destroyer796/VoyagerSplit/Pics/3dBack12-3.png

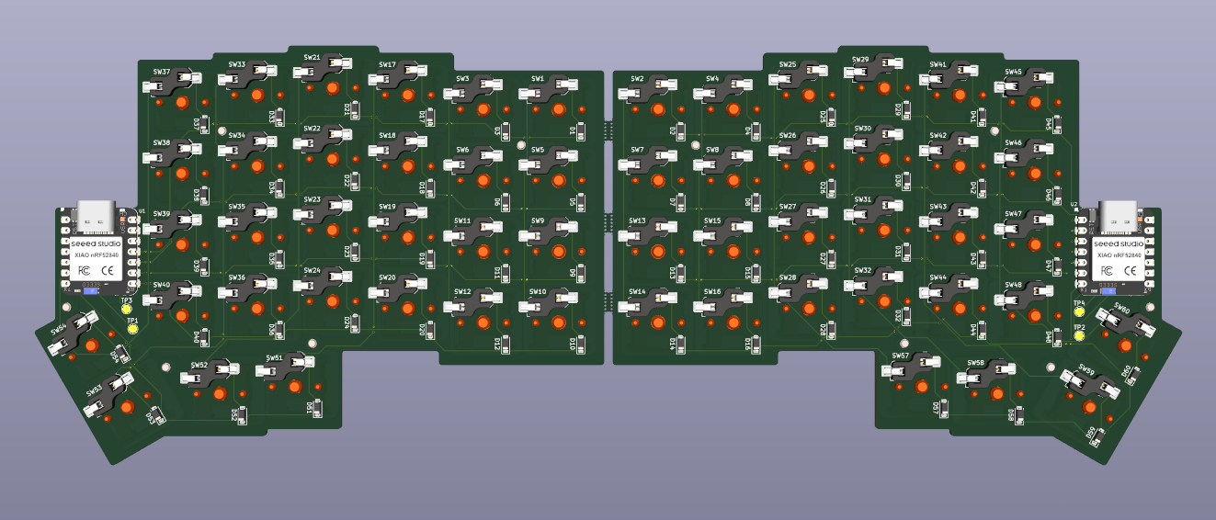
Pics/3dBack12-3.png
