destroyer796/VoyagerSplit/Pics/3DBack12-4.png

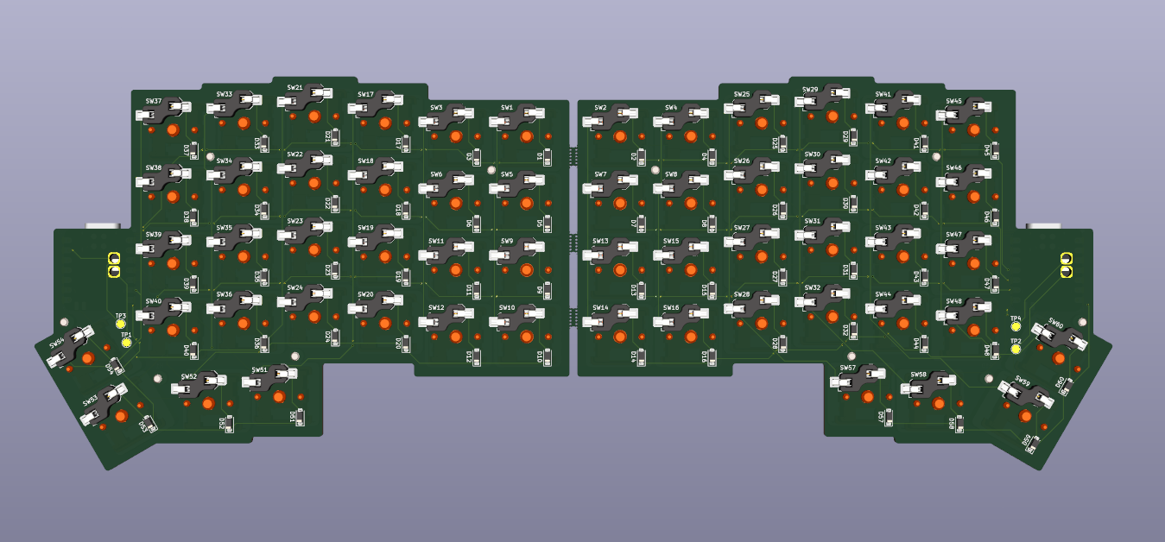
Pics/3DBack12-4.png
