destroyer796/VoyagerSplit/Pics/3DFront12-4.png

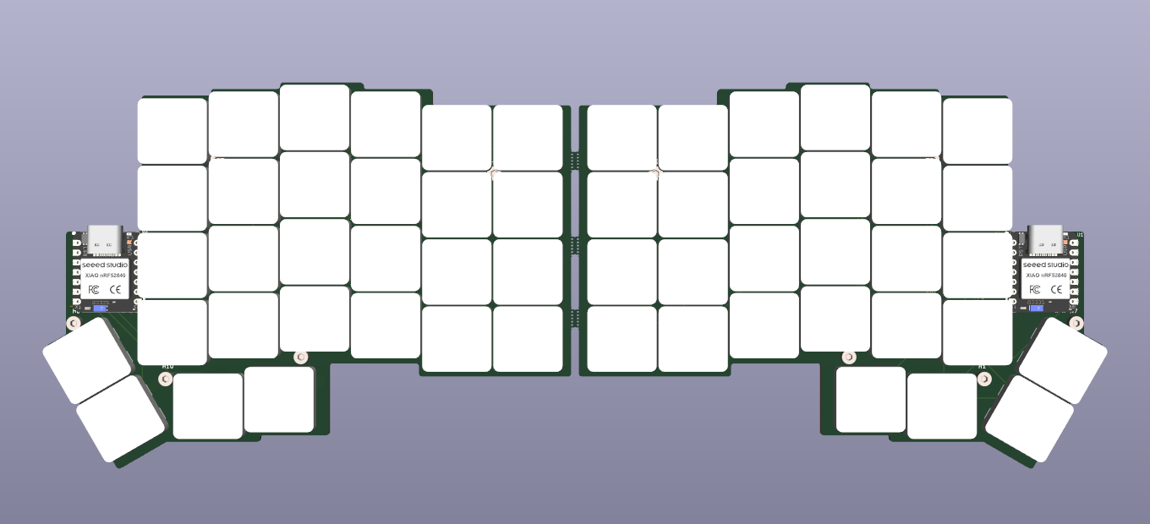
Pics/3DFront12-4.png
