destroyer796/VoyagerSplit/Pics/AliCart12-5.png

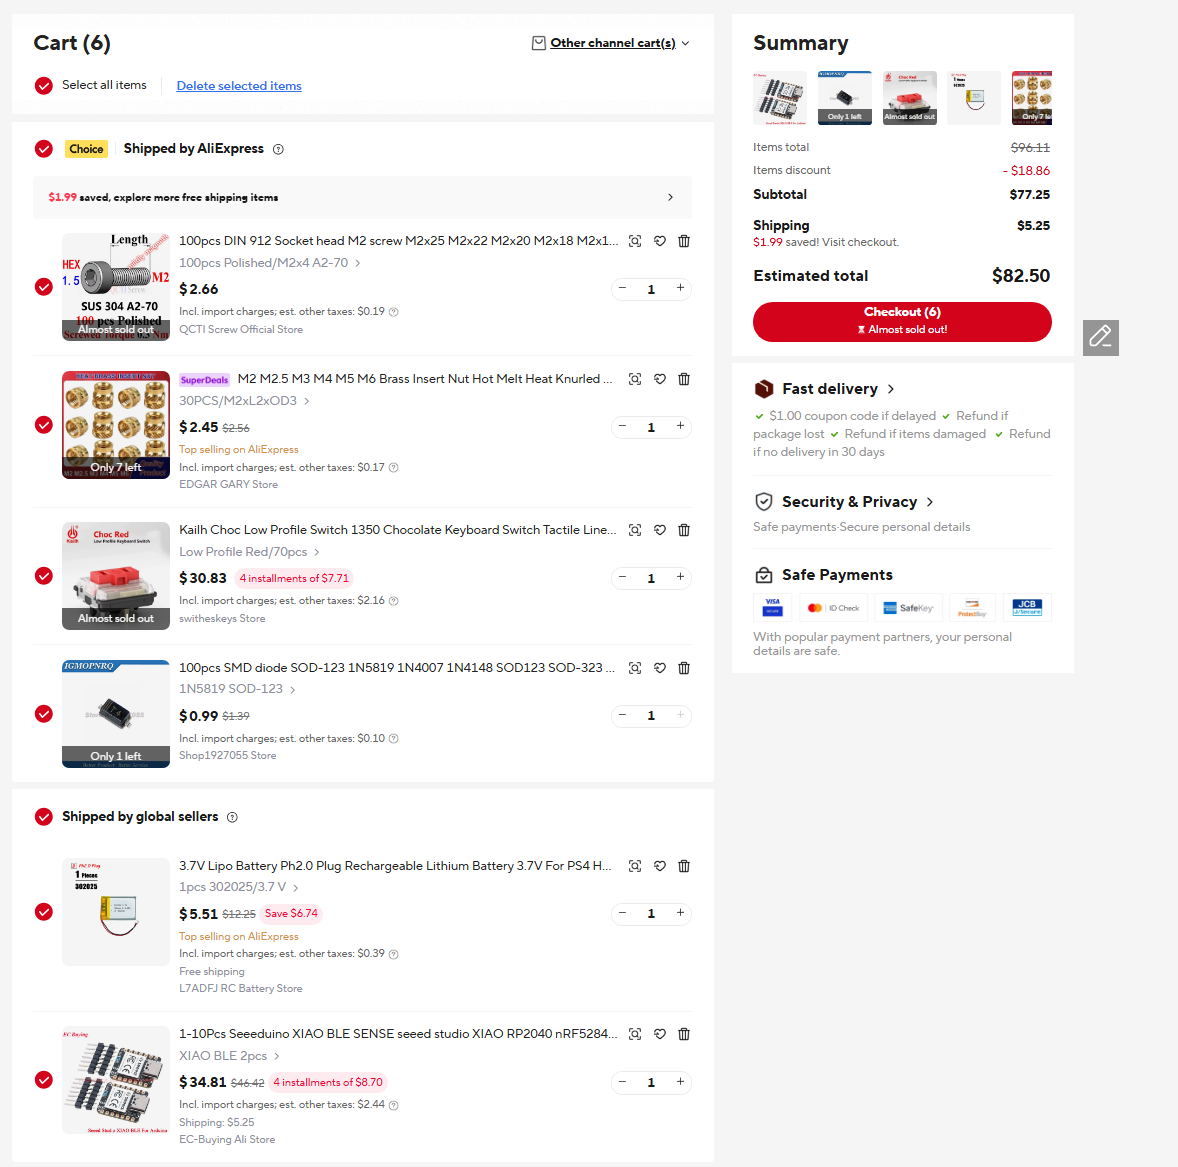
Pics/AliCart12-5.png
