destroyer796/VoyagerSplit/Pics/AliVoyagerCart2.png

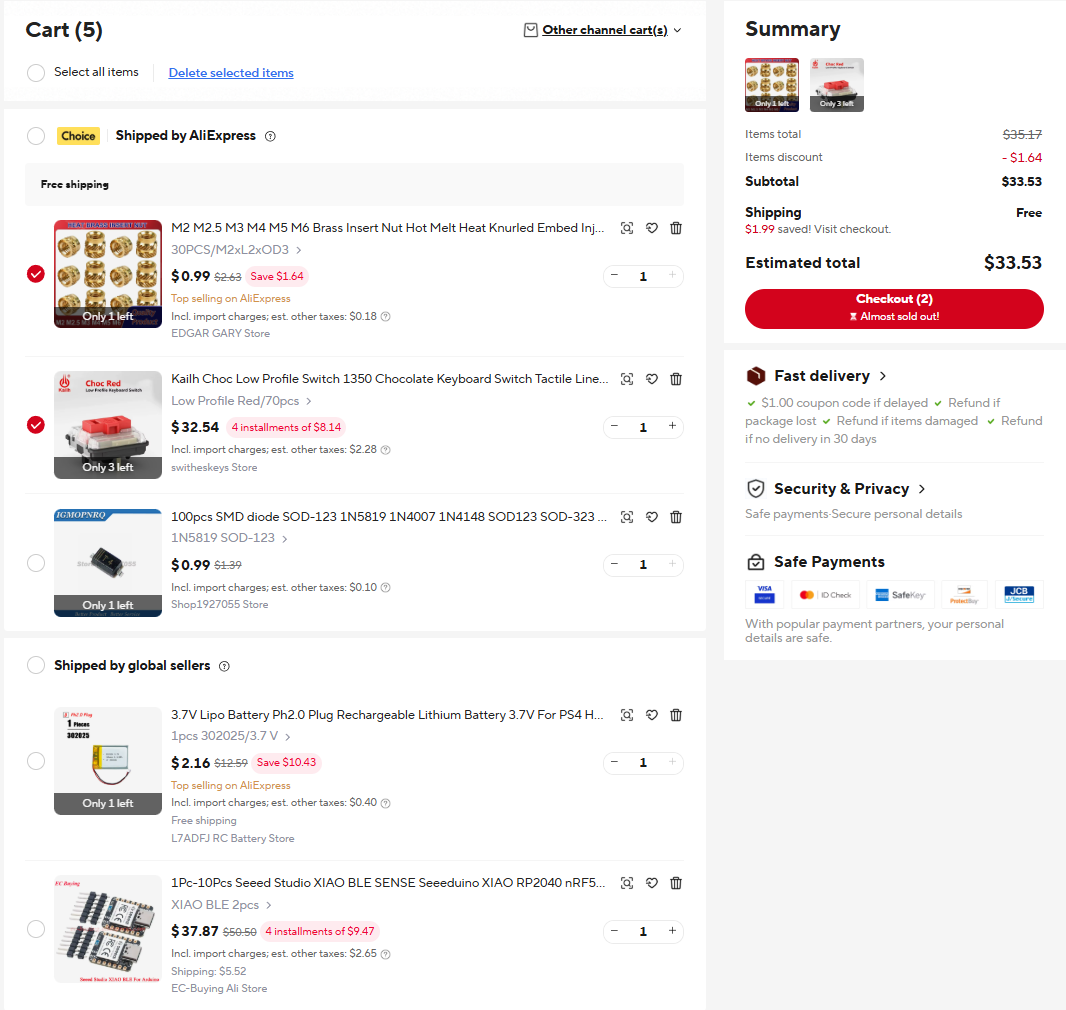
Pics/AliVoyagerCart2.png
