destroyer796/VoyagerSplit/Pics/AliVoyagerCart.png

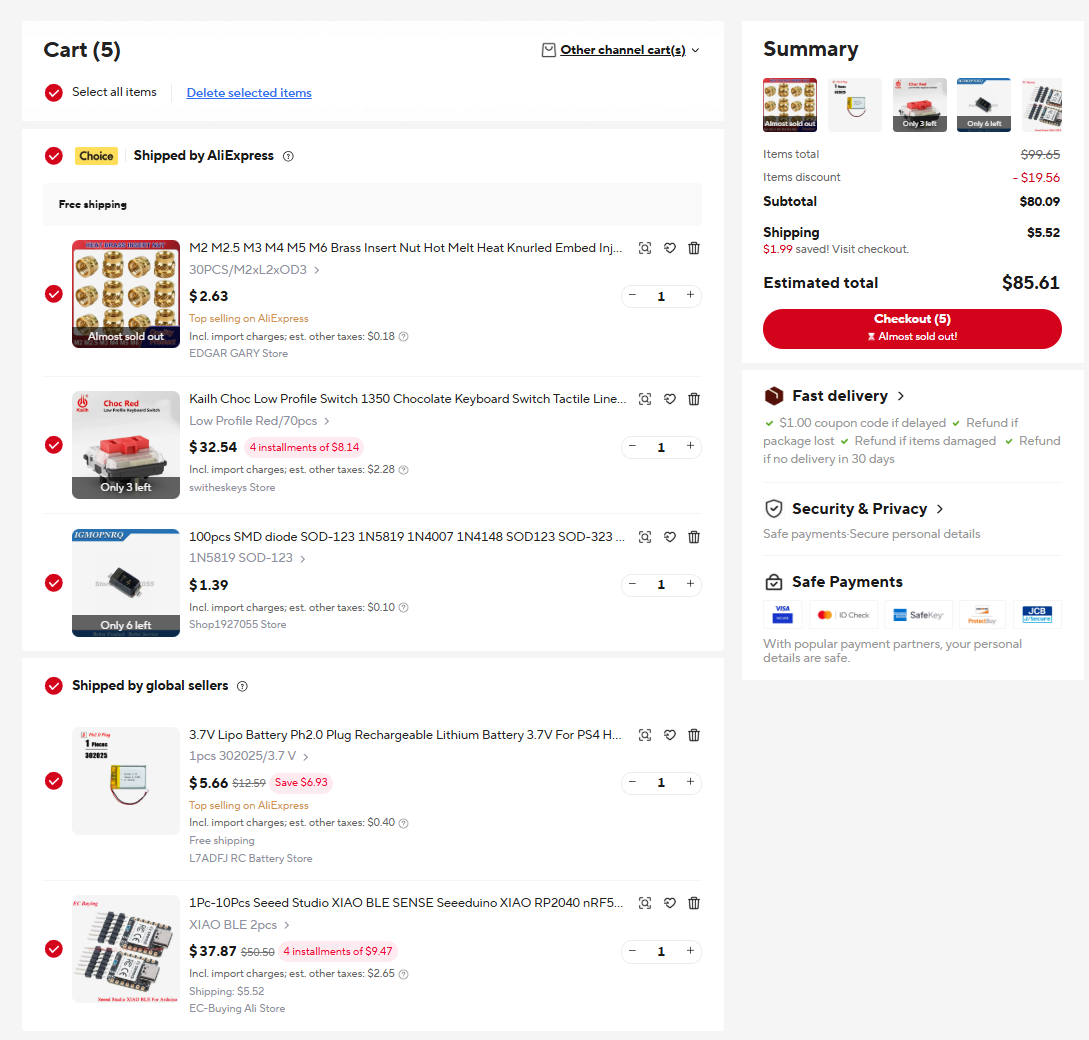
Pics/AliVoyagerCart.png
