destroyer796/VoyagerSplit/Pics/CADnewplate4-3.png

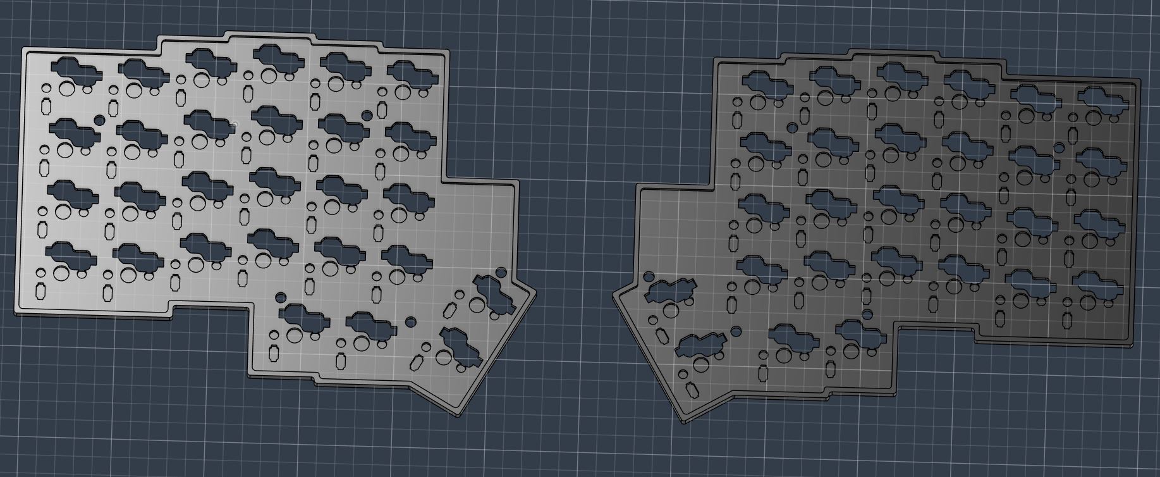
Pics/CADnewplate4-3.png
