destroyer796/VoyagerSplit/Pics/JLCCart12-5.png

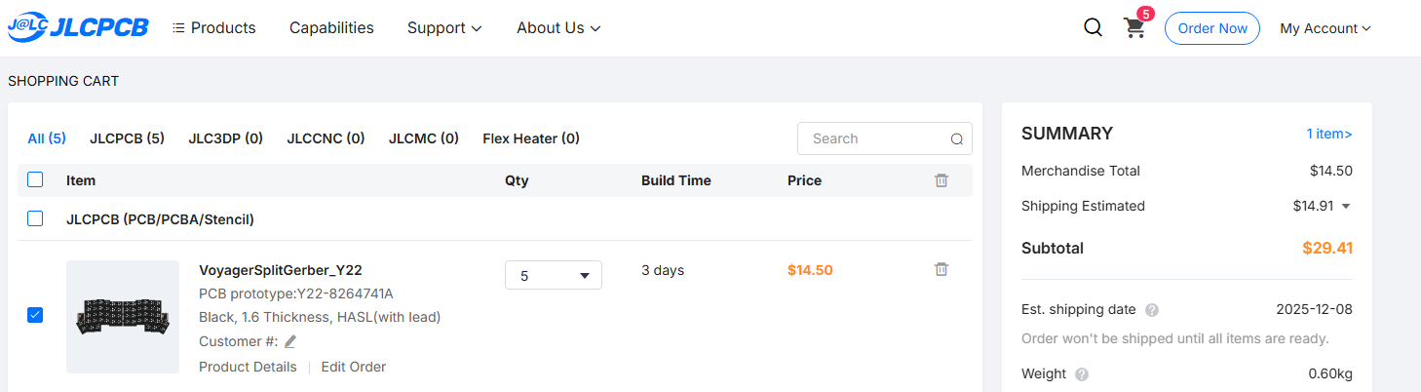
Pics/JLCCart12-5.png
