destroyer796/VoyagerSplit/Pics/JLCVoyager2.png

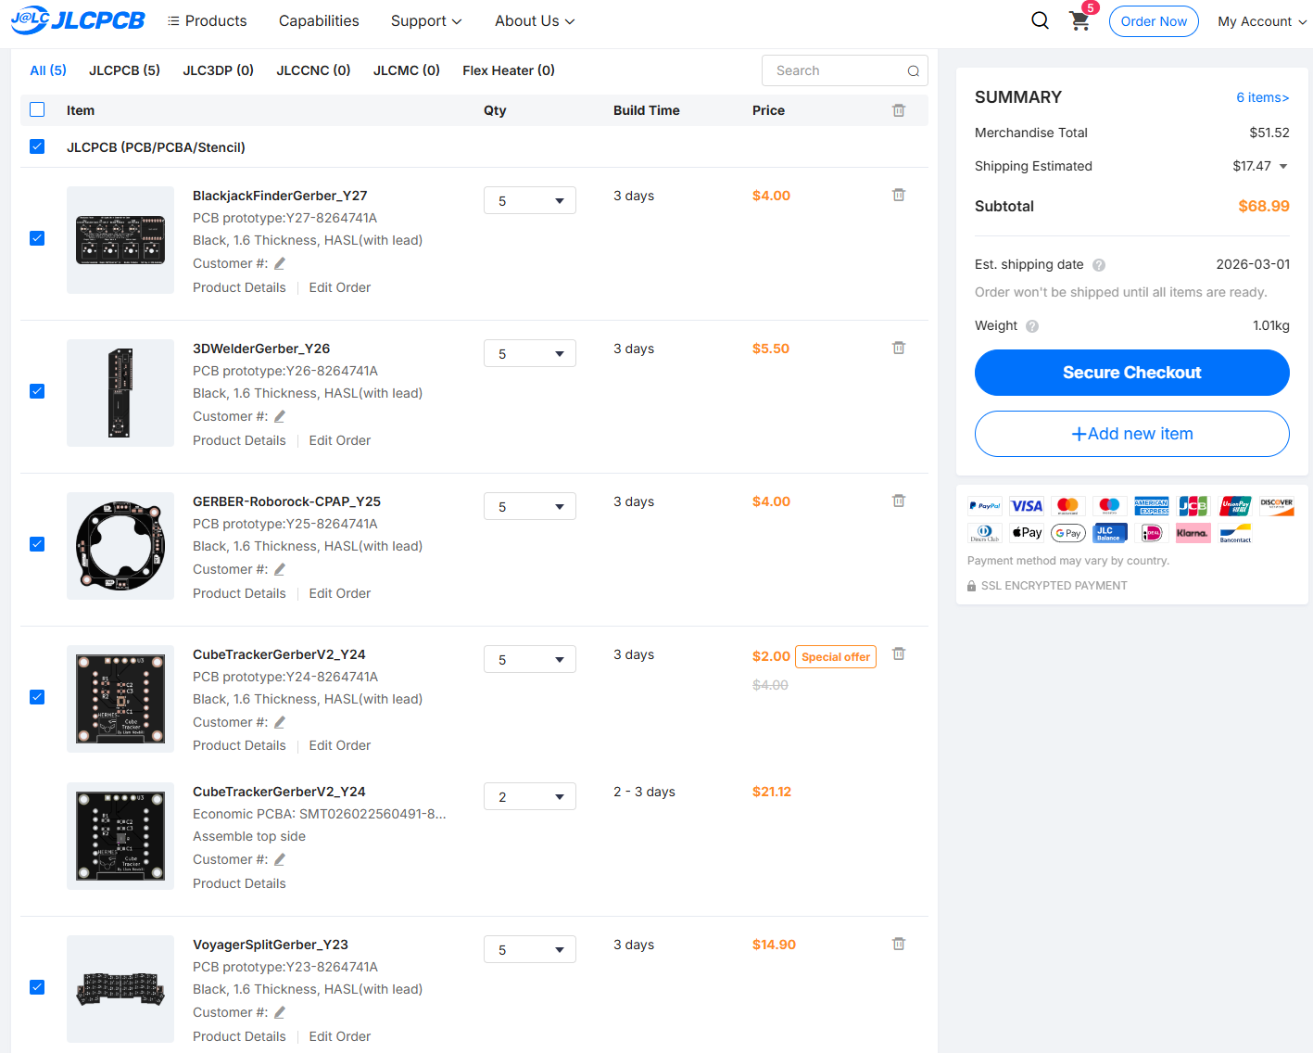
Pics/JLCVoyager2.png
