destroyer796/VoyagerSplit/Pics/PCB11-27.png

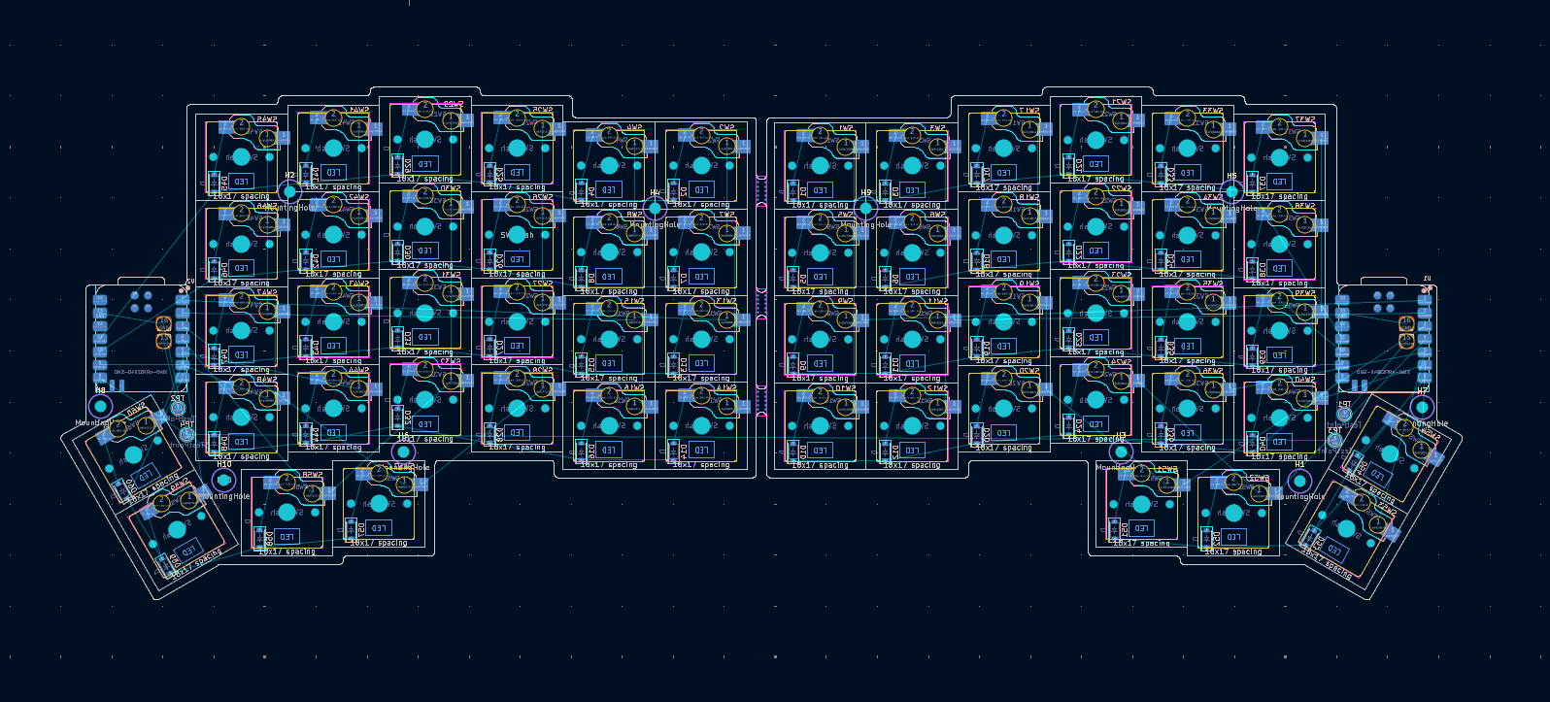
Pics/PCB11-27.png
