destroyer796/VoyagerSplit/Pics/PCB11-30.png

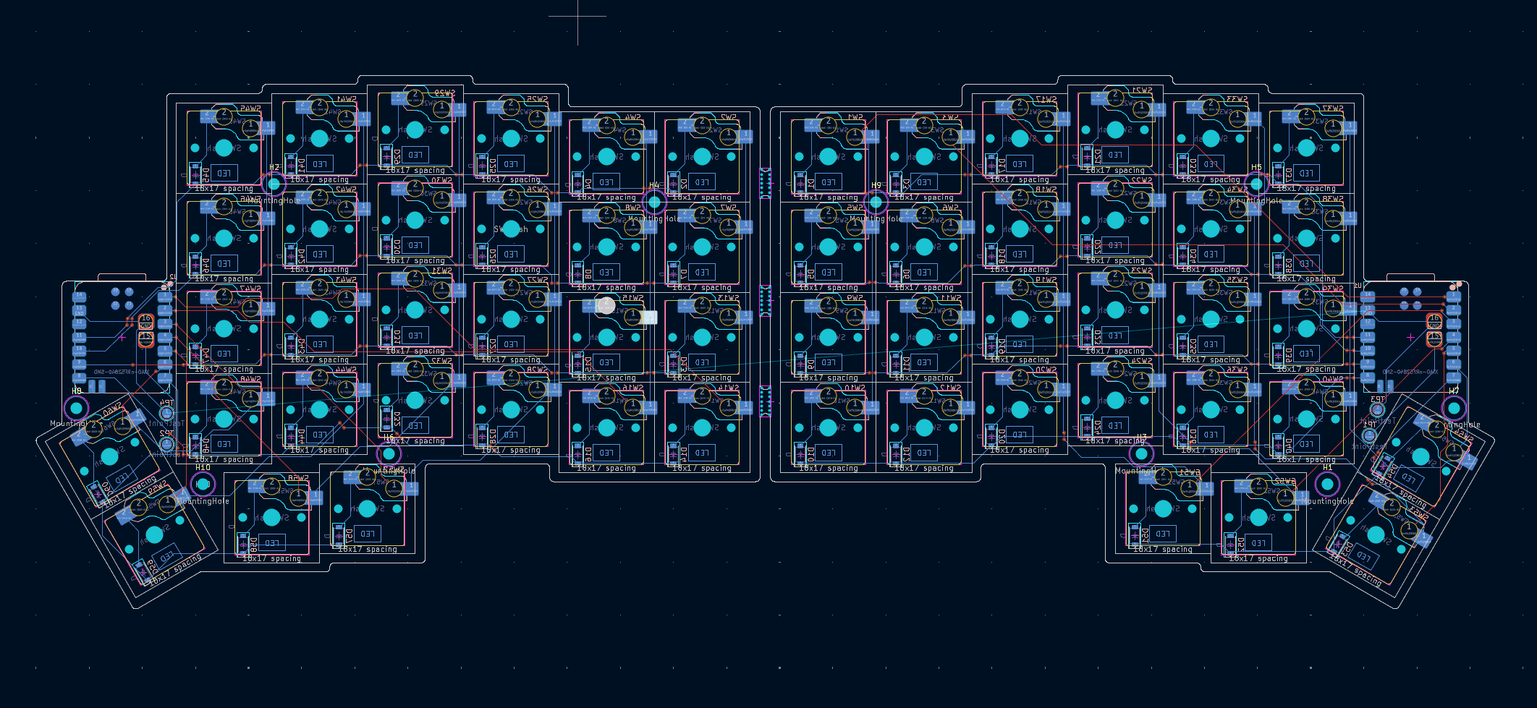
Pics/PCB11-30.png
