destroyer796/VoyagerSplit/Pics/PCB12-4.png

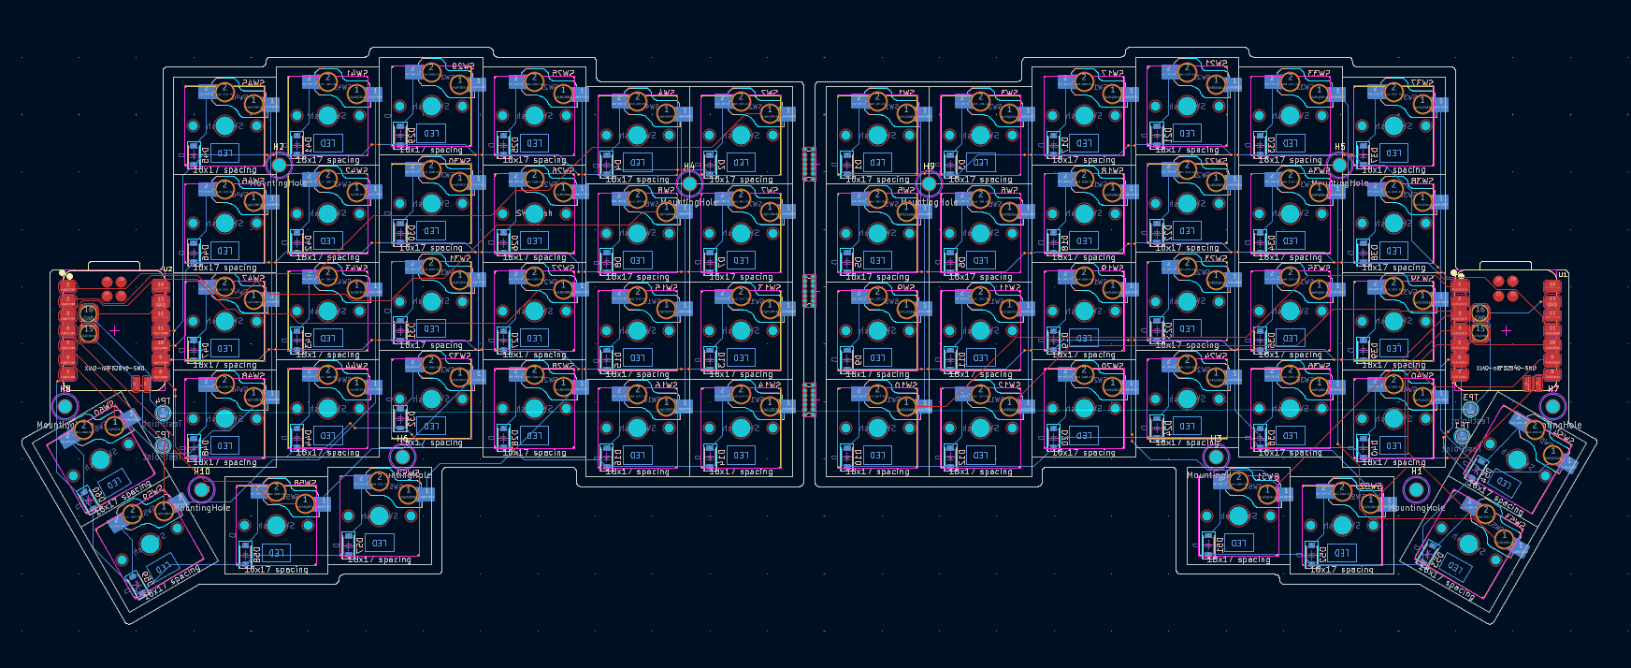
Pics/PCB12-4.png
