destroyer796/VoyagerSplit/Pics/RenderRoughFront12-5.png

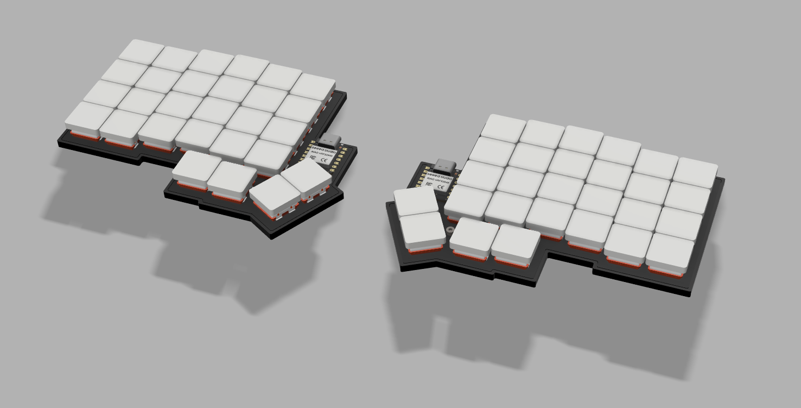
Pics/RenderRoughFront12-5.png
