destroyer796/VoyagerSplit/Pics/BOM12-4.png

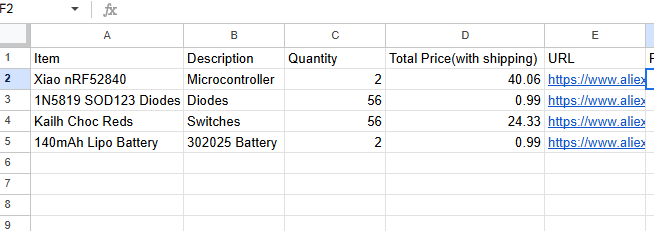
Pics/BOM12-4.png
