destroyer796/VoyagerSplit/Pics/SolderedBack3-31.jpg

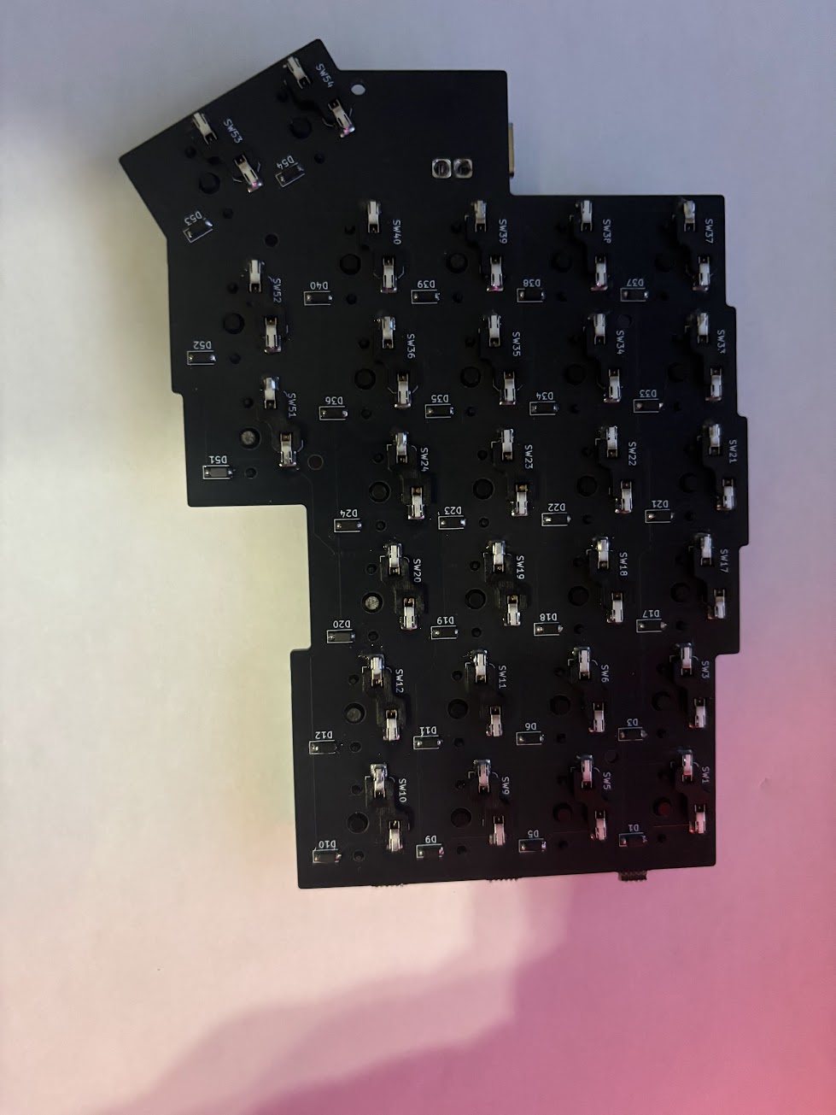
Pics/SolderedBack3-31.jpg
