destroyer796/VoyagerSplit/Pics/SolderedBack4-3.jpg

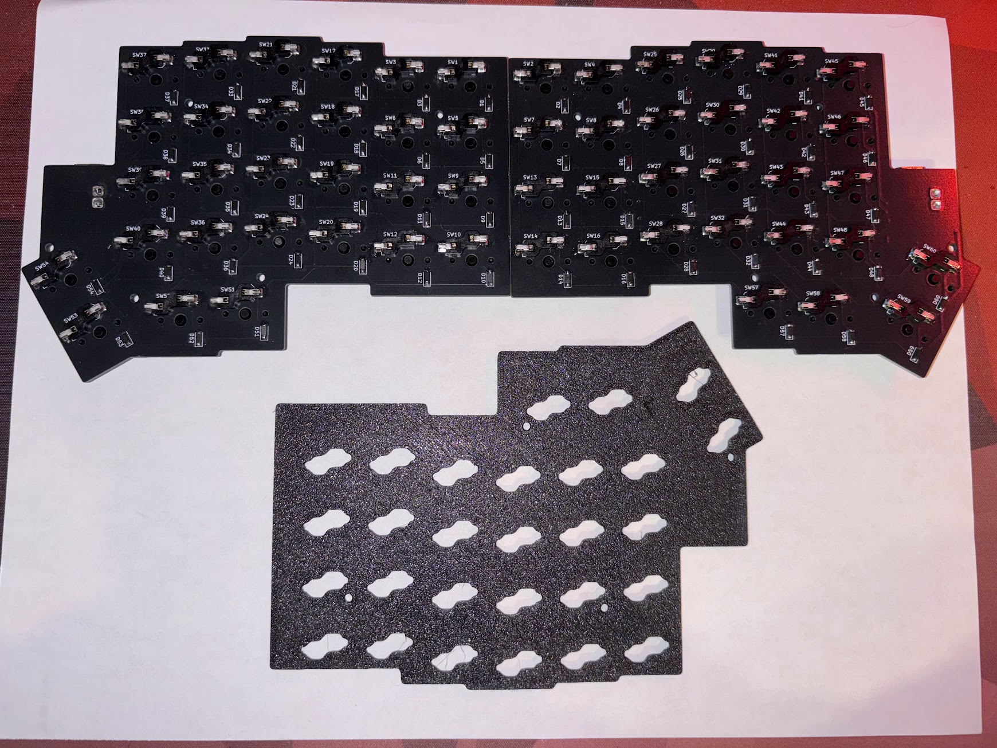
Pics/SolderedBack4-3.jpg
