destroyer796/VoyagerSplit/Pics/SolderedFront3-31.jpg

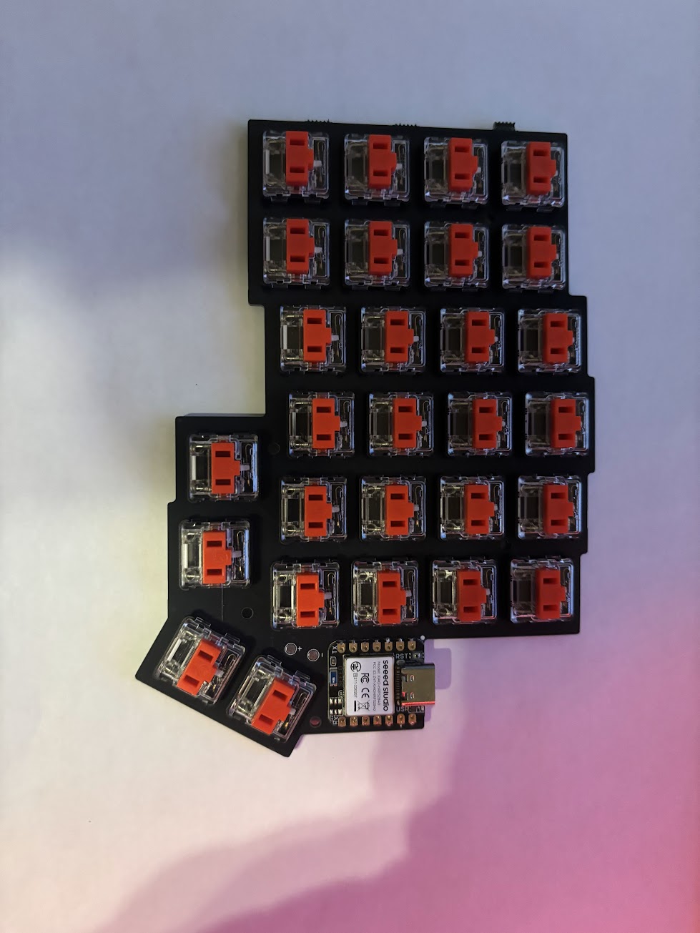
Pics/SolderedFront3-31.jpg
