destroyer796/VoyagerSplit/Pics/SolderedFront4-3.jpg

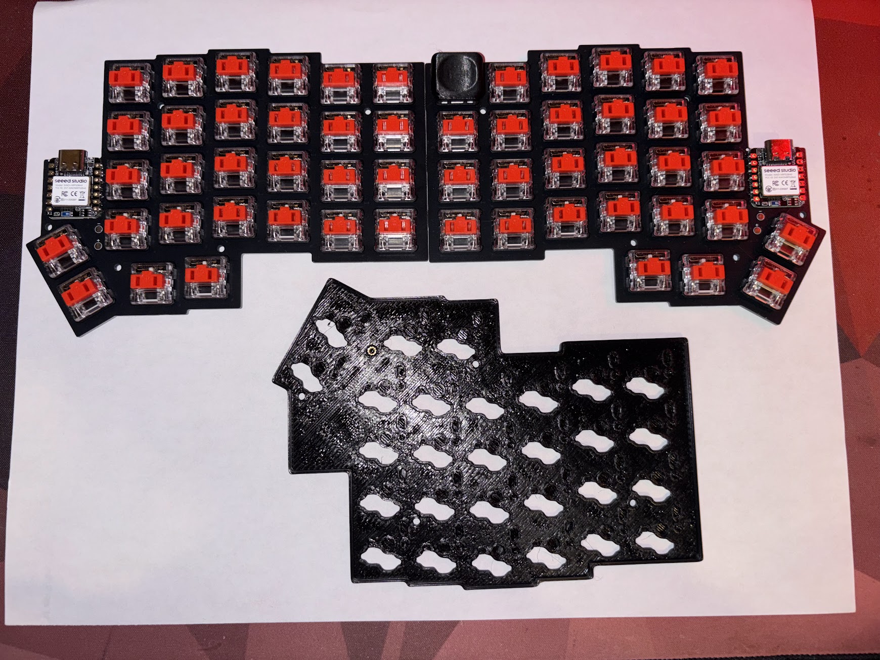
Pics/SolderedFront4-3.jpg
